SamerSafadi/CamaroSim/2021 Chevrolet Camaro Steering Column/1.webp

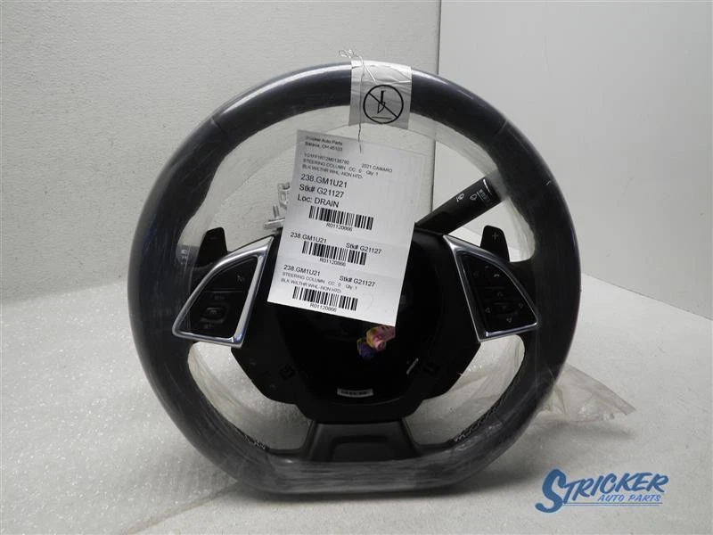
2021 Chevrolet Camaro Steering Column/1.webp
