SamerSafadi/CamaroSim/2021 Chevrolet Camaro Steering Column/2.webp

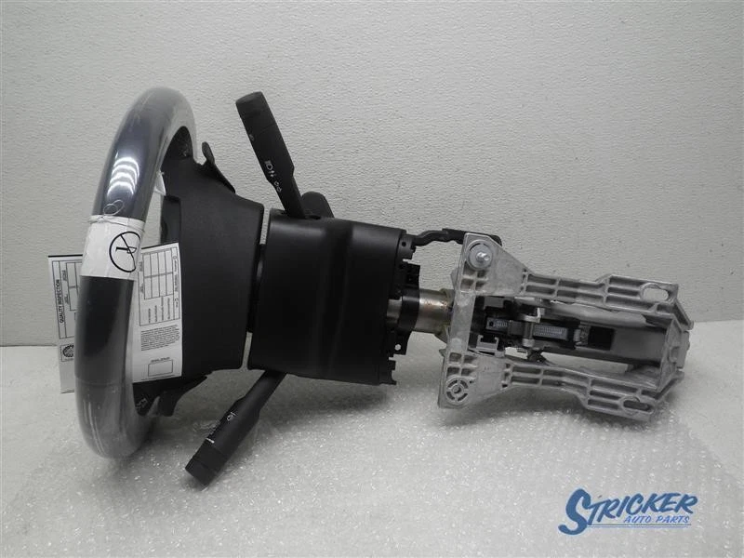
2021 Chevrolet Camaro Steering Column/2.webp
