SamerSafadi/CamaroSim/2021 Chevrolet Camaro Steering Column/3.webp

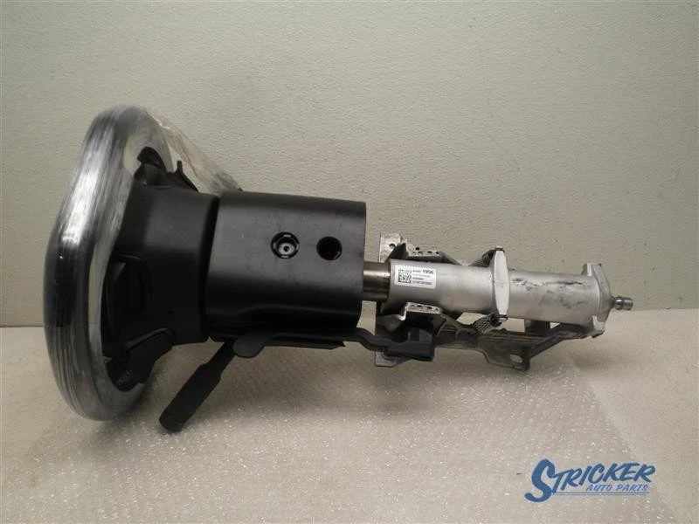
2021 Chevrolet Camaro Steering Column/3.webp
