SamerSafadi/CamaroSim/2021 Chevrolet Camaro Steering Column/5.webp

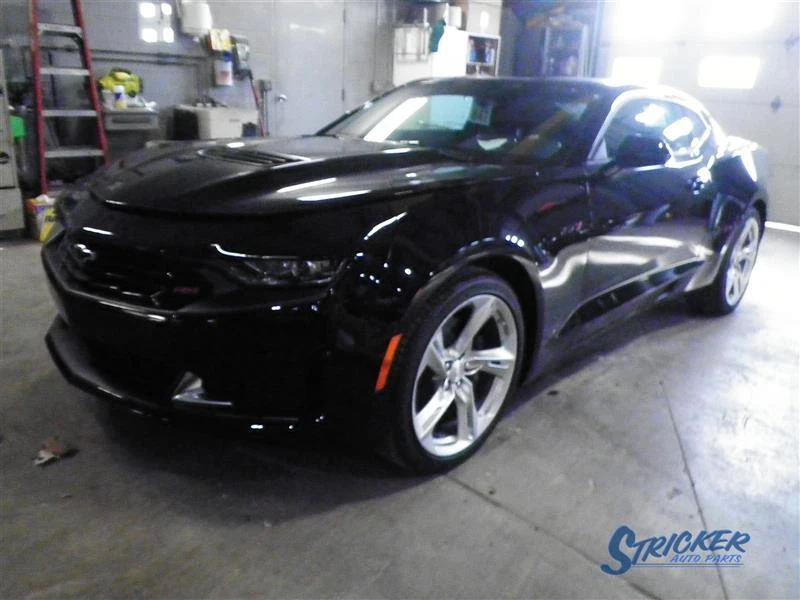
2021 Chevrolet Camaro Steering Column/5.webp
