SamerSafadi/CamaroSim/2021 Chevrolet Camaro Steering Column/6.webp

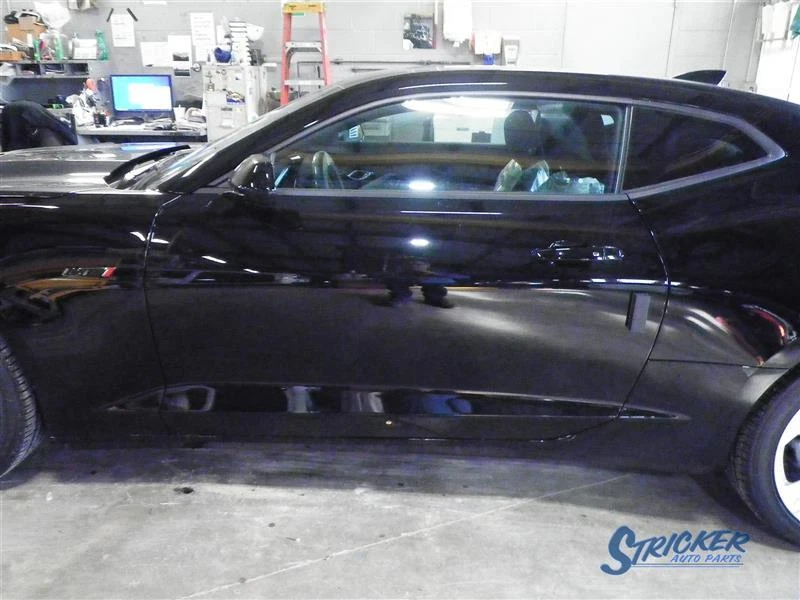
2021 Chevrolet Camaro Steering Column/6.webp
