SamerSafadi/CamaroSim/2021 Chevrolet Camaro Steering Column/7.webp

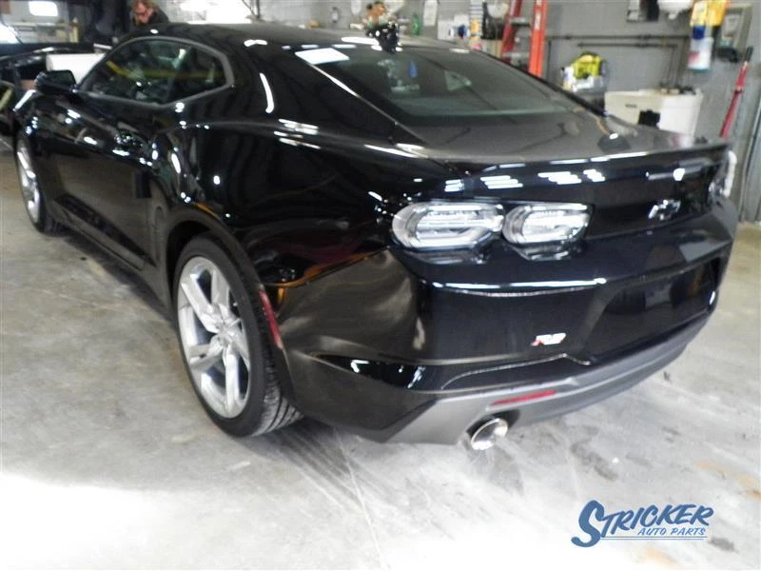
2021 Chevrolet Camaro Steering Column/7.webp
