SamerSafadi/CamaroSim/2021 Chevrolet Camaro Steering Column/8.webp

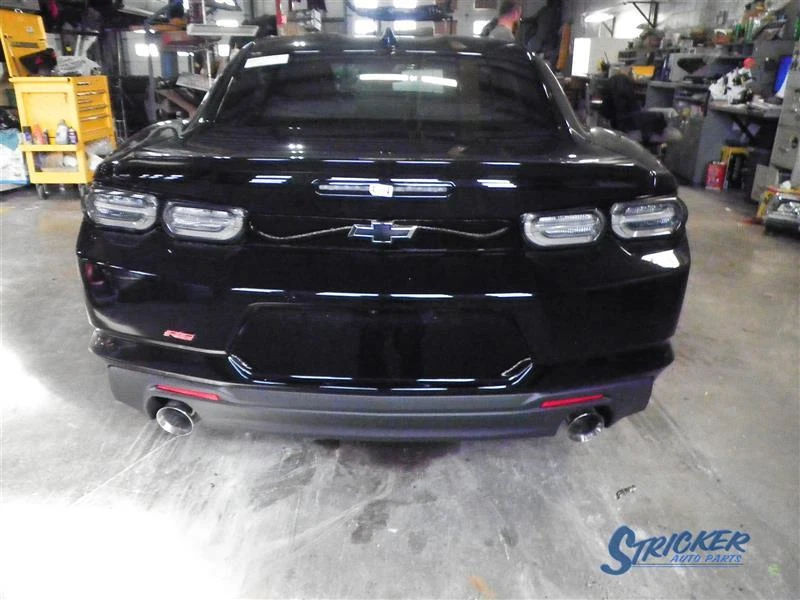
2021 Chevrolet Camaro Steering Column/8.webp
