SamerSafadi/CamaroSim/2021 Chevrolet Camaro Steering Column/9.webp

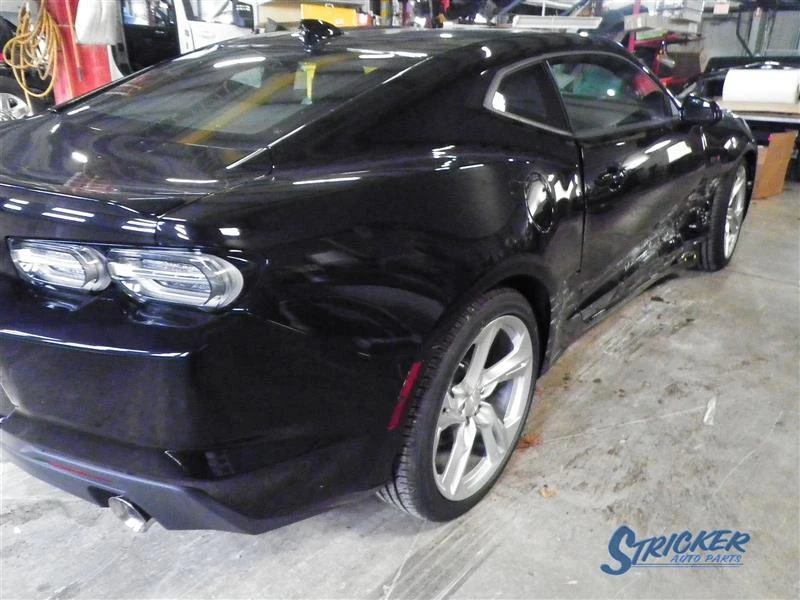
2021 Chevrolet Camaro Steering Column/9.webp
