SamerSafadi/CamaroSim/2021 Chevrolet Camaro Steering Column/10.webp

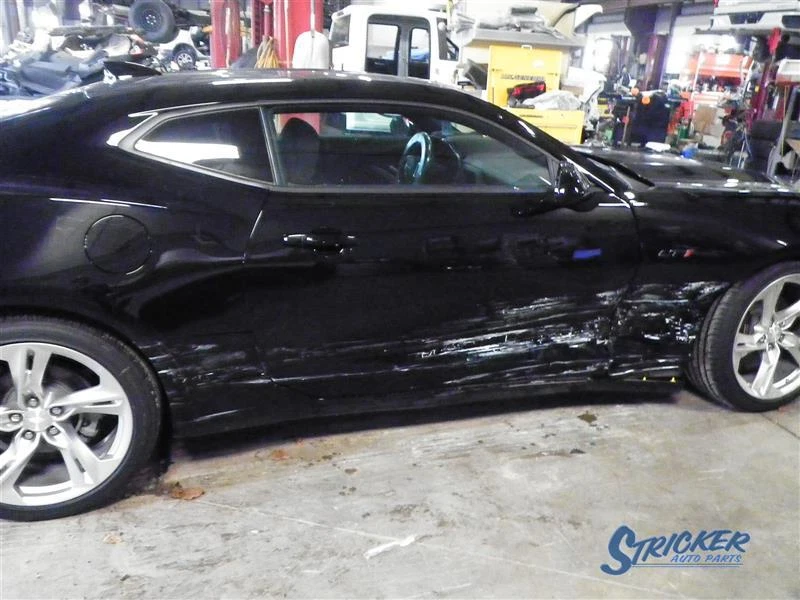
2021 Chevrolet Camaro Steering Column/10.webp
