SamerSafadi/CamaroSim/2021 Chevrolet Camaro Steering Column/11.webp

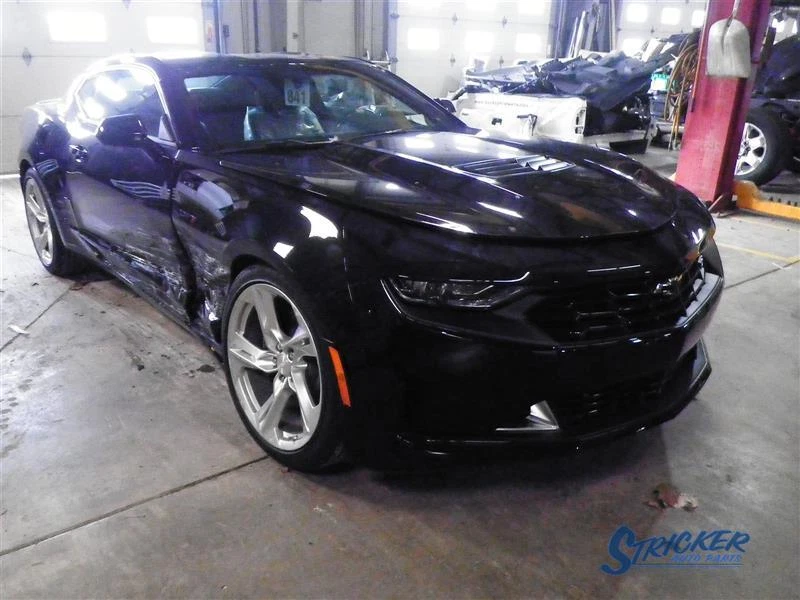
2021 Chevrolet Camaro Steering Column/11.webp
