SamerSafadi/CamaroSim/2021 Chevrolet Camaro Steering Column/12.webp

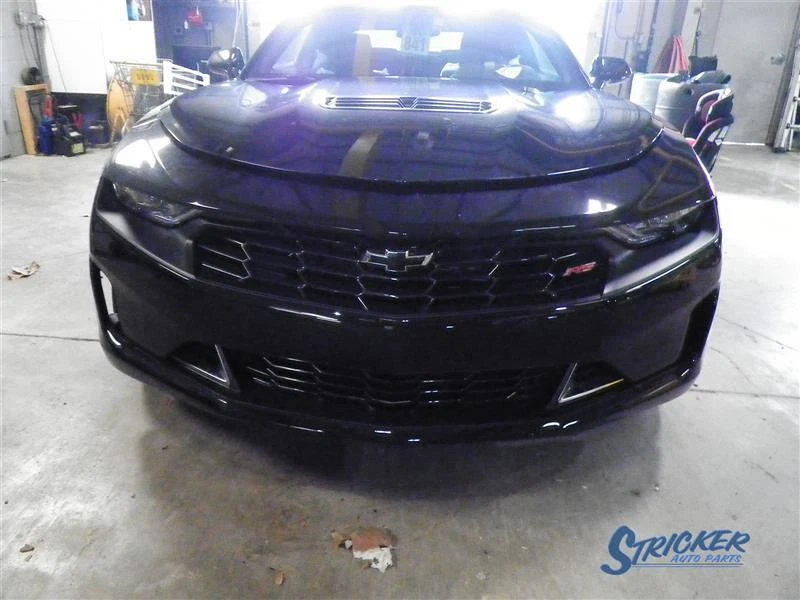
2021 Chevrolet Camaro Steering Column/12.webp
