SamerSafadi/CamaroSim/2021 Chevrolet Camaro Steering Column/13.webp

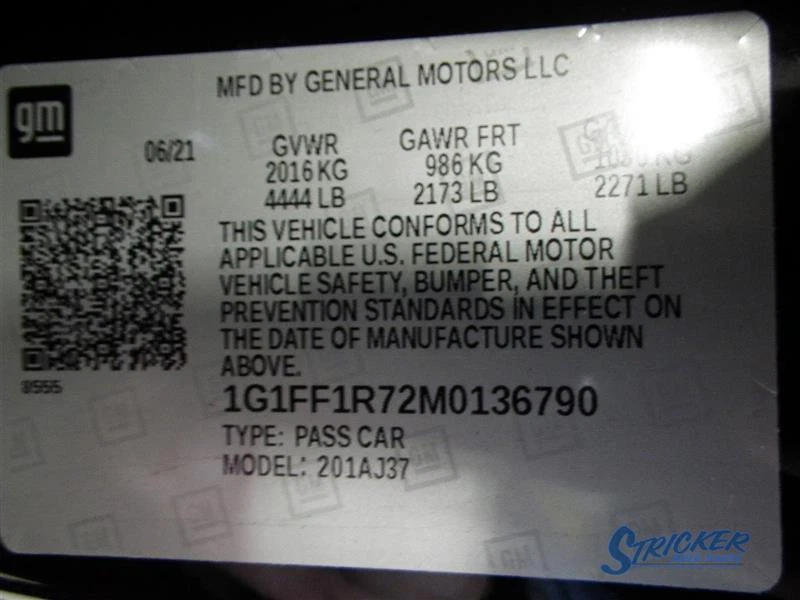
2021 Chevrolet Camaro Steering Column/13.webp
