SamerSafadi/CamaroSim/2021 Chevrolet Camaro Steering Column/14.webp

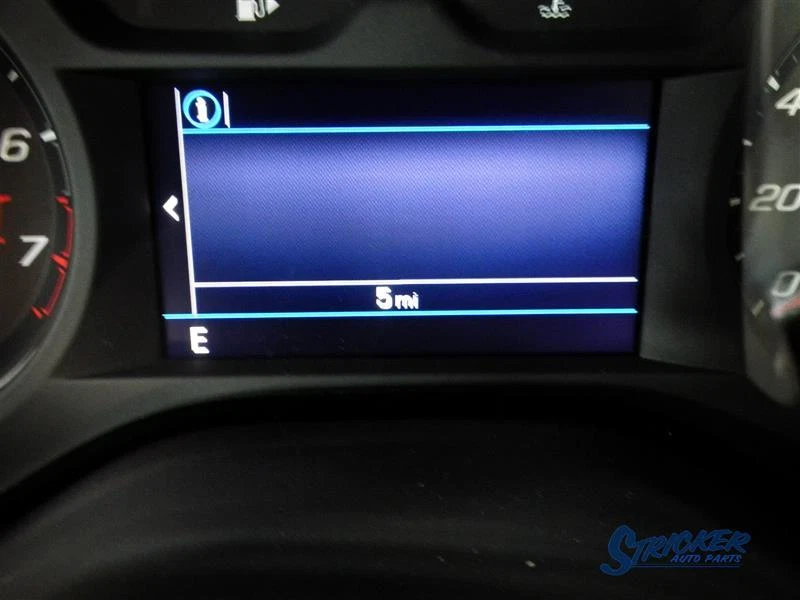
2021 Chevrolet Camaro Steering Column/14.webp
