SamerSafadi/CamaroSim/2021 Chevrolet Camaro Steering Column/15.webp

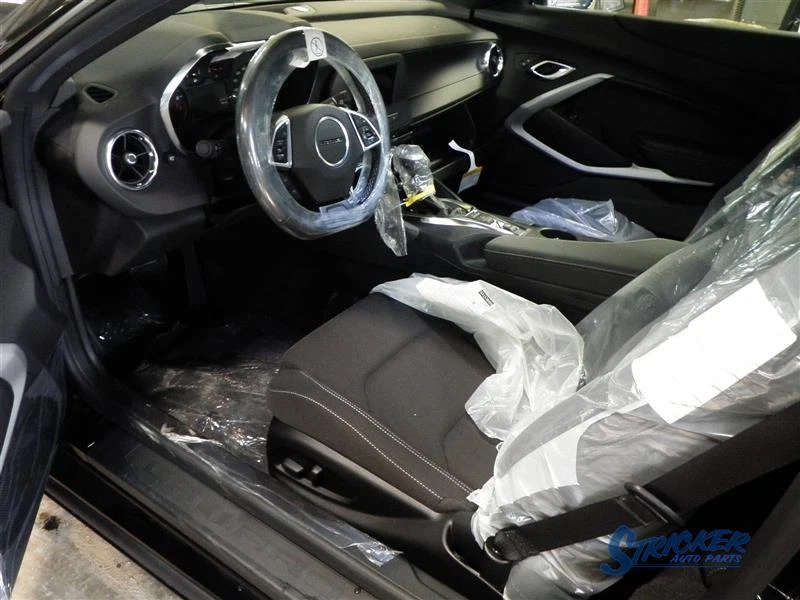
2021 Chevrolet Camaro Steering Column/15.webp
