SamerSafadi/CamaroSim/2021 Chevrolet Camaro Steering Column/16.webp

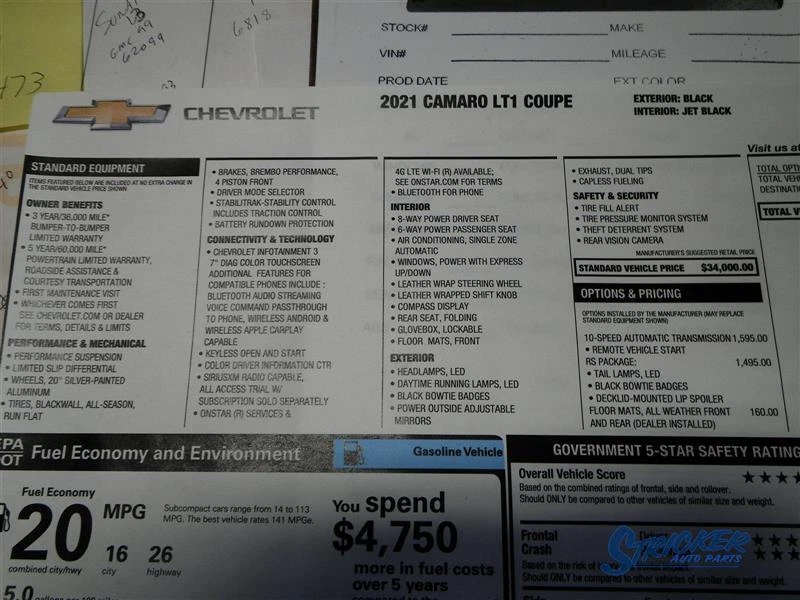
2021 Chevrolet Camaro Steering Column/16.webp
