SamerSafadi/CamaroSim/2021 Chevrolet Camaro Steering Column/17.webp

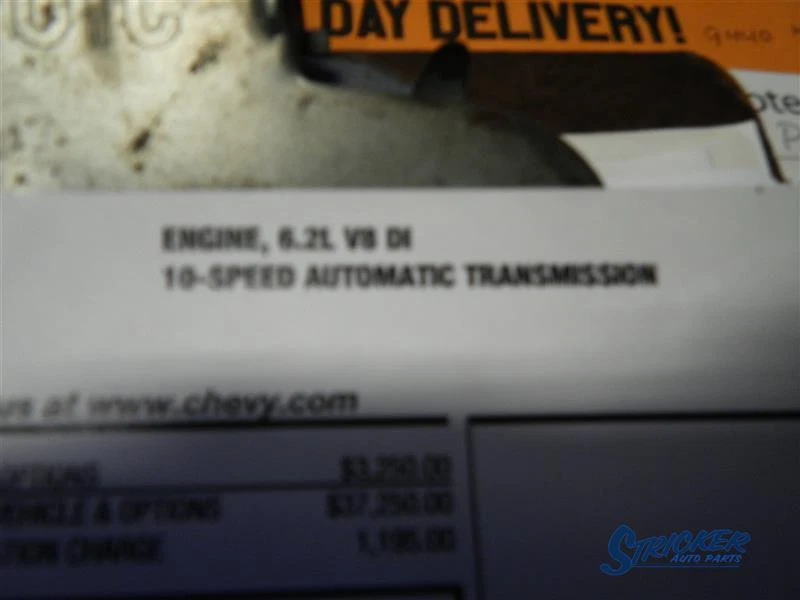
2021 Chevrolet Camaro Steering Column/17.webp
