SamerSafadi/CamaroSim/2021 Chevrolet Camaro Steering Column/18.webp

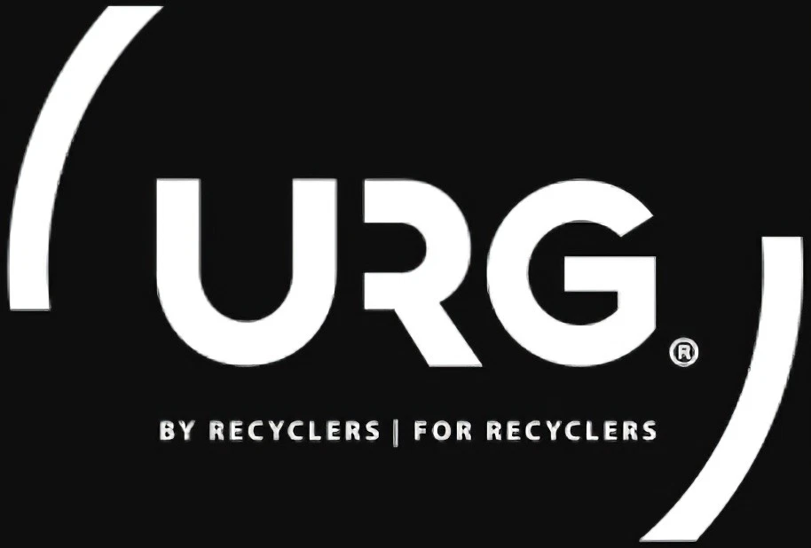
2021 Chevrolet Camaro Steering Column/18.webp
