SamerSafadi/CamaroSim/ProMicro USB-C for Arduino/min-3-1.jpg

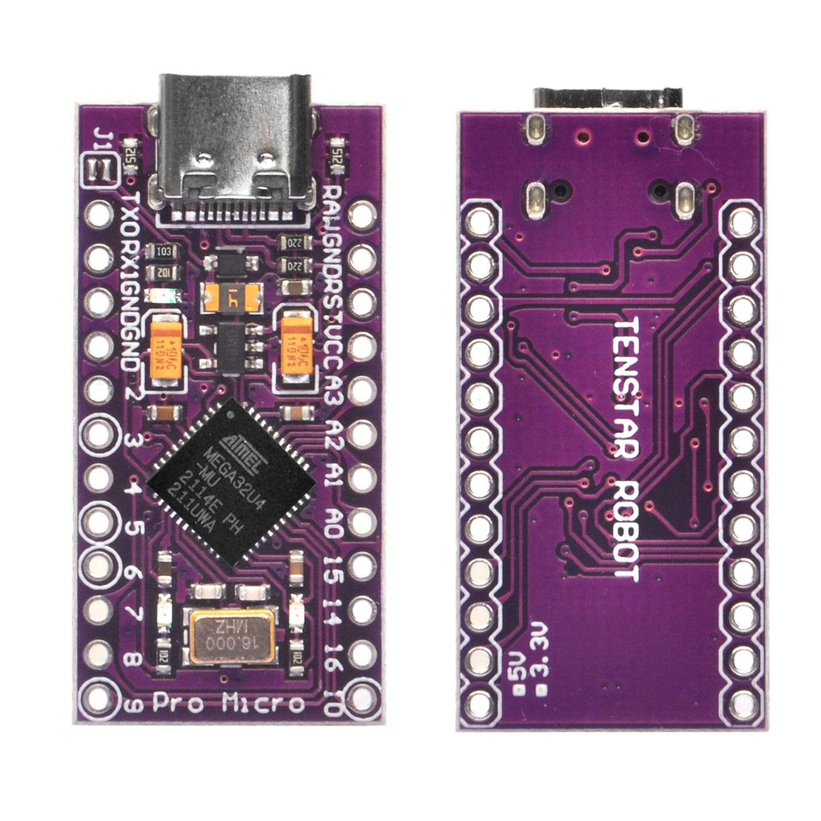
ProMicro USB-C for Arduino/min-3-1.jpg
