SamerSafadi/CamaroSim/ProMicro USB-C for Arduino/min-4.jpg

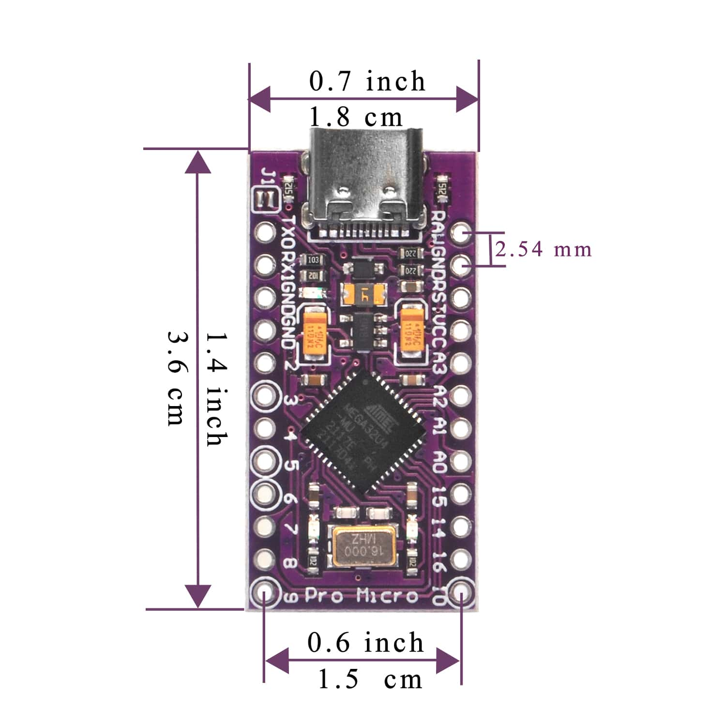
ProMicro USB-C for Arduino/min-4.jpg
